ykeara/hardware_vivetrackerbattery/pics/2.jpg

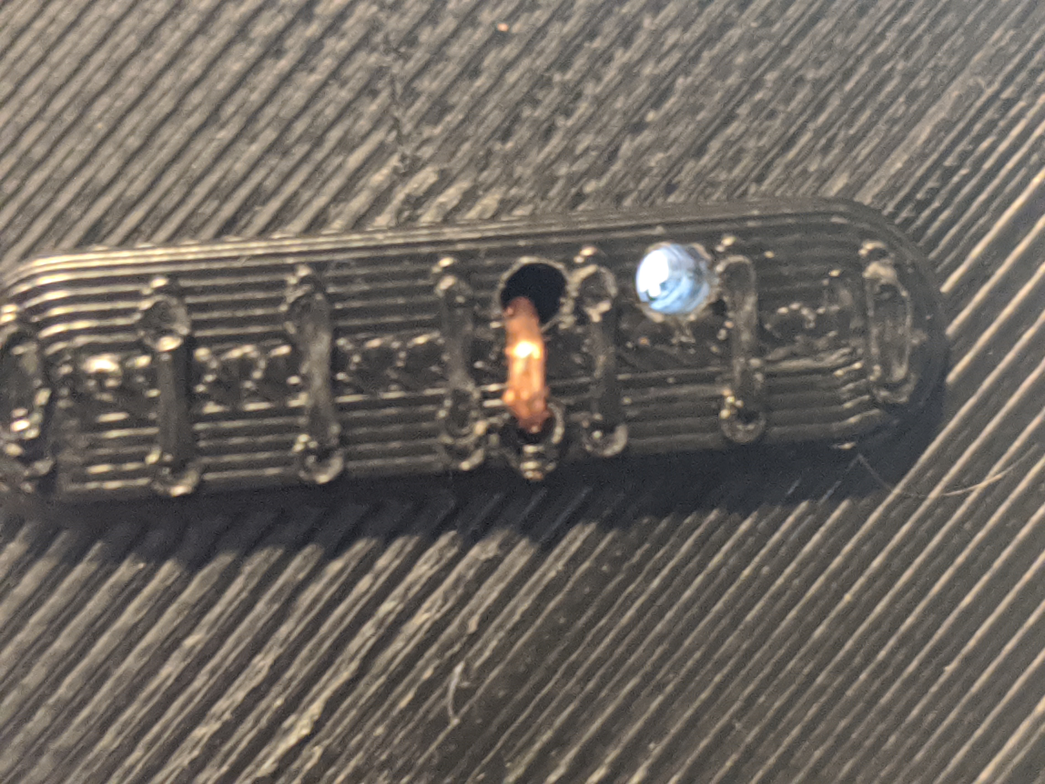
pics/2.jpg
