ykeara/hardware_vivetrackerbattery/pics/3.jpg

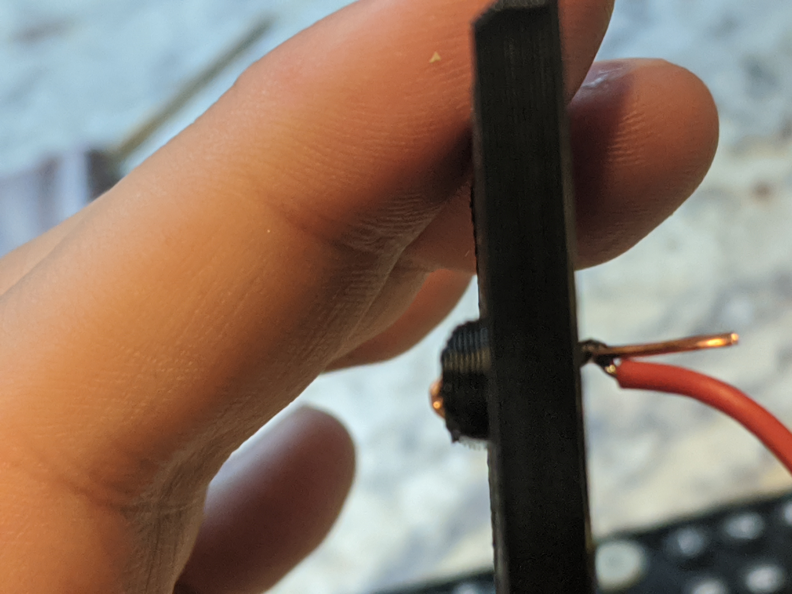
pics/3.jpg
