ykeara/hardware_vivetrackerbattery/pics/8.jpg

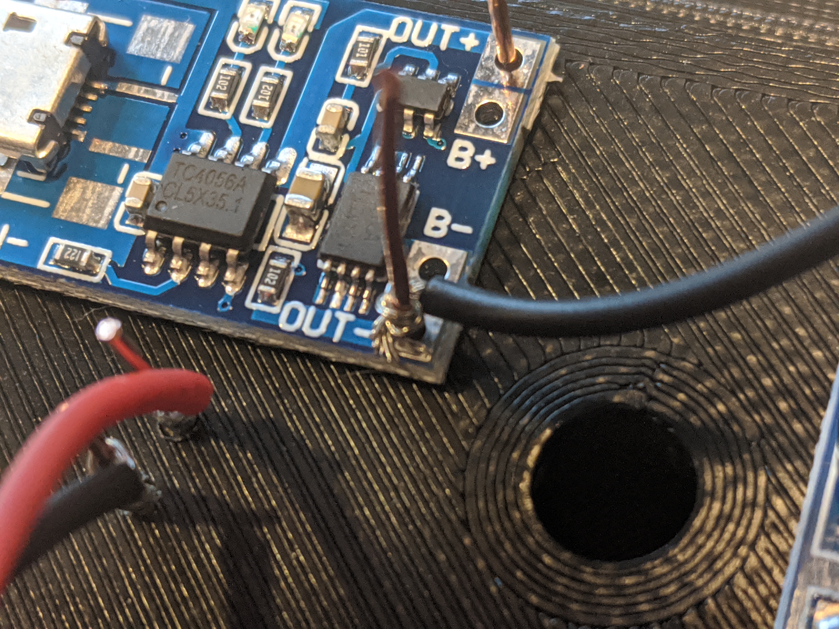
pics/8.jpg
