ykeara/hardware_vivetrackerbattery/pics/9.jpg

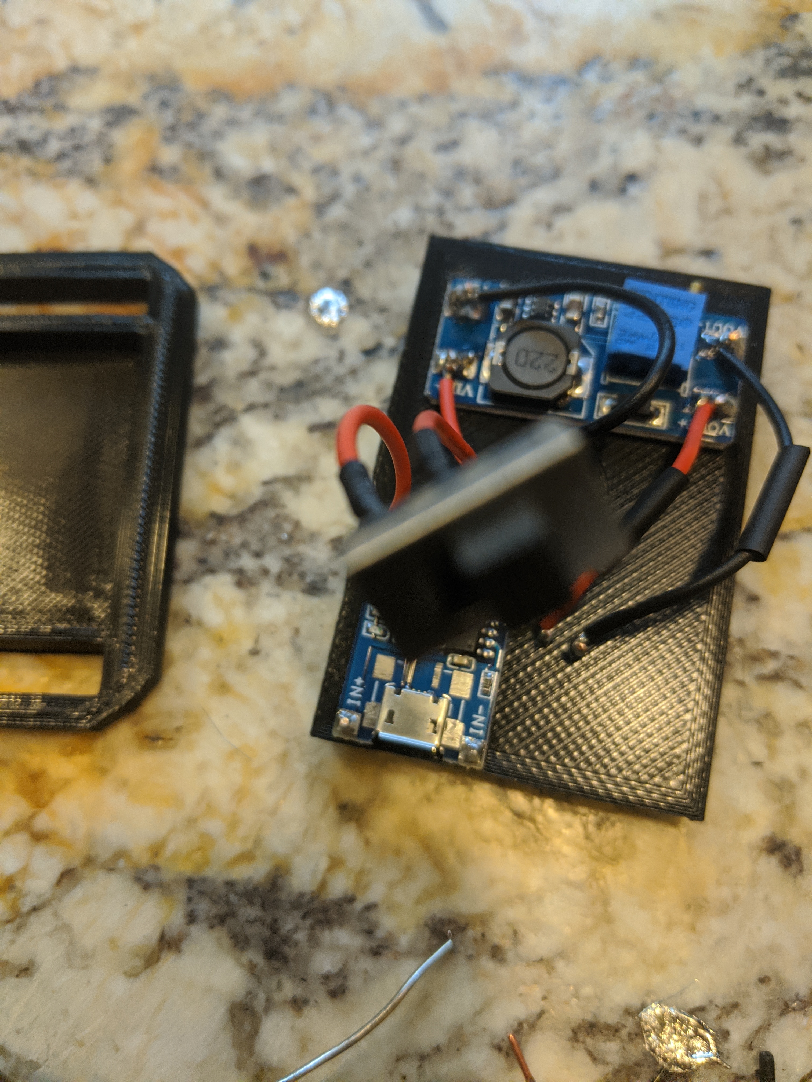
pics/9.jpg
